ARQMS/arqms-device/firmware/main/Control/PushBtn/PushBtnCtrlTask.h

#ifndef PUSH_BTN_CTRL_TASK_H_
#define PUSH_BTN_CTRL_TASK_H_

// Platform include
#include <HumiDevice.Platform/Platform.h>
#include <HumiDevice.Rtos/TaskBase.h>
#include <HumiDevice.Rtos/EventPublisherMultiple.h>
#include <HumiDevice.Rtos/TimerEvent.h>

// Project includes
#include "Events/ButtonEvent.h"
#include "ButtonSM.h"
#include "ButtonSMIfc.h"


/**
 * This unit is called in the case of a push button event
 * 
 * @see https://github.com/ARQMS/arqms-device/wiki/Firmware#decomposition
 */
class PushBtnCtrlTask : public TaskBase<2, sizeof(ButtonEvent)>, public ButtonSMIfc {
public:
    EventPublisherMultiple<2> Control;

public:
    /**
     * Constructor
     */
    PushBtnCtrlTask();

    /**
     * Destructor
     */
    ~PushBtnCtrlTask();

    /**
     * @see ButtonSMIfc::onButtonPressed
     */
    virtual void onButtonPressed(const ButtonId id, const ButtonStatus status) override;

protected:
    /**
     * @see TaskBase::onInitialize()
     */
    virtual void onInitialize();

    /**
     * @see TaskBase::onStart()
     */
    virtual void onStart();

    /**
     * @see TaskBase::onExecute()
     */
    virtual void onHandleEvent(EventId eventId, Deserializer* pEvent = NULL) override;
    virtual void onHandleTimer(TimerId timerId) override;

private:
    // Helper
    void onHandleButtonEvent(const ButtonEvent& event);

    // Members
    ButtonSM m_swRstBtn;
    ButtonSM m_usrBtn;
};


#endif // PUSH_BTN_CTRL_TASK_H_
