ARQMS/arqms-device/firmware/main/HumiPlatform.h

#ifndef PLATFORM_H
#define PLATFORM_H

// Include compiler library
#include <stdint.h>
#include <string.h>

typedef float float32_t;
typedef bool bool_t;

// IDF includes
#include "esp_err.h"
#include "esp_log.h"

#endif // PLATFORM_H
