ARQMS/arqms-device/firmware/main/GuiUpdater/GuiUpdaterTask.cpp

#include "GuiUpdaterTask.h"

#include <HumiDevice.Platform/Math.h>

#include "Drivers/ApplicationHardwareConfig.h"
#include "Events/EventIdentifiers.h"
#include "Events/DisplayInfoEvent.h"

GuiUpdaterTask::GuiUpdaterTask() :
    Control(),
    m_airIndicator(LED_AIR_GOOD, LED_AIR_MOD, LED_AIR_POOR),
    m_ctrlIndicator(0, LED_WLAN),
    m_pRefreshTimer(NULL) {
}

GuiUpdaterTask::~GuiUpdaterTask() {
}

void GuiUpdaterTask::onInitialize()  {
    m_pRefreshTimer = createPeriodicTimer(REFRESH_RATE);
    m_pDelayTimer = createOneShotTimer(DELAY_MS);

    m_ctrlIndicator.initialize();

    m_ctrlIndicator.disable();
    m_airIndicator.disable();
}

void GuiUpdaterTask::onStart() {
    // nothing to do
}

void GuiUpdaterTask::onHandleEvent(EventId eventId, Deserializer* pEvent) {
    switch (eventId) {
        case EventIdentifiers::QUALITY_EVENT: 
            onHandleAirQuality(AirQualityEvent(*pEvent));
            break;

        case EventIdentifiers::WIFI_STATUS_EVENT: 
            onHandleWifiStatus(WifiStatusEvent(*pEvent));
            break;

        case EventIdentifiers::SENSOR_DATA_EVENT: 
            onHandleSensorData(SensorDataEvent(*pEvent));
            break;
        
        case EventIdentifiers::SENSOR_STATUS_EVENT: 
            onHandleSensorStatus(SensorStatusEvent(*pEvent));
            break;

        case EventIdentifiers::DEVICE_BTN_EVENT: 
            onHandleButton(ButtonEvent(*pEvent));
            break;

    default:
        break;
    }
}

void GuiUpdaterTask::onHandleTimer(const TimerId timerId) {
    if (m_pRefreshTimer->id == timerId) {
        onHandleRefresh();
    }
    else if (m_pDelayTimer->id == timerId) {
        onHandleDelay();
    }
}

void GuiUpdaterTask::onHandleAirQuality(const AirQualityEvent& qualityEvent) {
    m_airIndicator.setQuality(qualityEvent.getQuality());
}

void GuiUpdaterTask::onHandleSensorData(const SensorDataEvent& data) {
    // nothing to do
}

void GuiUpdaterTask::onHandleWifiStatus(const WifiStatusEvent& wifiStatus) {
    if (wifiStatus.getStatus() == WifiStatus::CLIENT_SEARCHING) {
        m_ctrlIndicator.setColor({0, 0, 255}, 500);
    }
    if (wifiStatus.getStatus() == WifiStatus::CONNECTING) {
        m_ctrlIndicator.setColor({0, 0, 255}, 100);
    }
    else if (wifiStatus.getStatus() == WifiStatus::CLIENT_CONNECTED) {
        m_ctrlIndicator.setColor({0, 0, 255});
    } 
    else if (wifiStatus.getStatus() == WifiStatus::CONNECTED) {
        m_ctrlIndicator.setColor({0, 0, 50}, 100);
    } 
    else if (wifiStatus.getStatus() == WifiStatus::MQTT_CONNECTED) {
        // blue indicator is calculated based on following article
        // https://www.metageek.com/training/resources/understanding-rssi/
        const uint32_t blue = Math::truncateToRange(Math::linearMap((int)wifiStatus.getRssi(), -90, -50, 50, 255), 0, 255);
        m_ctrlIndicator.setColor({0, 0, blue});
    }
    else if (wifiStatus.getStatus() == WifiStatus::MQTT_DISCONNECTED) {
        m_ctrlIndicator.setColor({0, 0, 50}, 100);
    } 
    else if (wifiStatus.getStatus() == WifiStatus::UNKNOWN_ERROR) {
        enable();

        m_ctrlIndicator.setColor({255, 0, 0}, 100);
    }
}

void GuiUpdaterTask::onHandleSensorStatus(const SensorStatusEvent& status) {
    if (status.getStatus() == SensorStatus::ACQUIRE) {
        m_ctrlIndicator.setColor({255, 255, 0}, 50);
    }
    else if (status.getStatus() == SensorStatus::IDLE) {
        m_ctrlIndicator.setColor({0, 0, 255});
    }
    else if (status.getStatus() == SensorStatus::ERROR) {
        enable();

        m_ctrlIndicator.setColor({255, 0, 0}, 100);
    }
}

void GuiUpdaterTask::onHandleRefresh() {
    m_ctrlIndicator.refresh();
    m_airIndicator.refresh();
}

void GuiUpdaterTask::onHandleDelay() {
    disable();
}

void GuiUpdaterTask::onHandleButton(const ButtonEvent& button) {
    if (button.getButtonId() == ButtonId::USER) {
        enable();
    }
}

void GuiUpdaterTask::disable() {
    m_ctrlIndicator.disable();
    m_airIndicator.disable();

    m_pRefreshTimer->stop();

    DisplayInfoEvent event(false);
    Control.send(EventIdentifiers::DISPLAY_INFO_EVENT, &event);
}

void GuiUpdaterTask::enable() {
    m_ctrlIndicator.enable();
    m_airIndicator.enable();

    m_pRefreshTimer->start();
    m_pDelayTimer->start();
        
    DisplayInfoEvent event(true);
    Control.send(EventIdentifiers::DISPLAY_INFO_EVENT, &event);
}
